iteam1/jetboy/docs/assets/imgs/img3.png

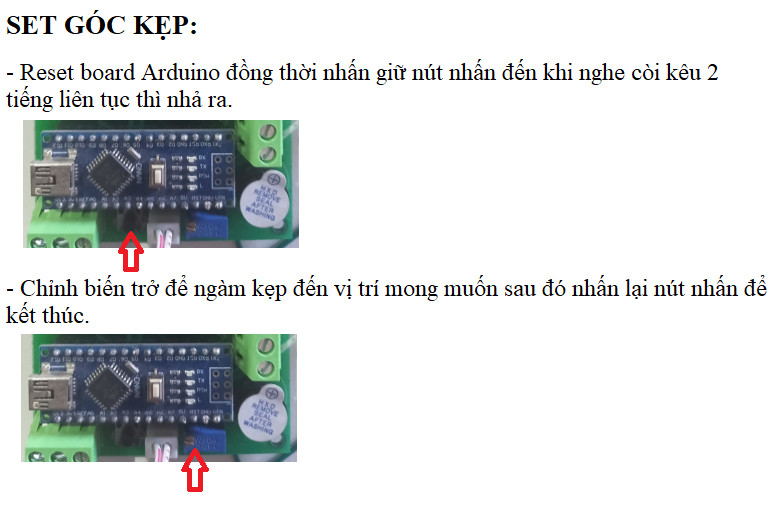
docs/assets/imgs/img3.png
