iteam1/jetboy/docs/assets/imgs/img4.png

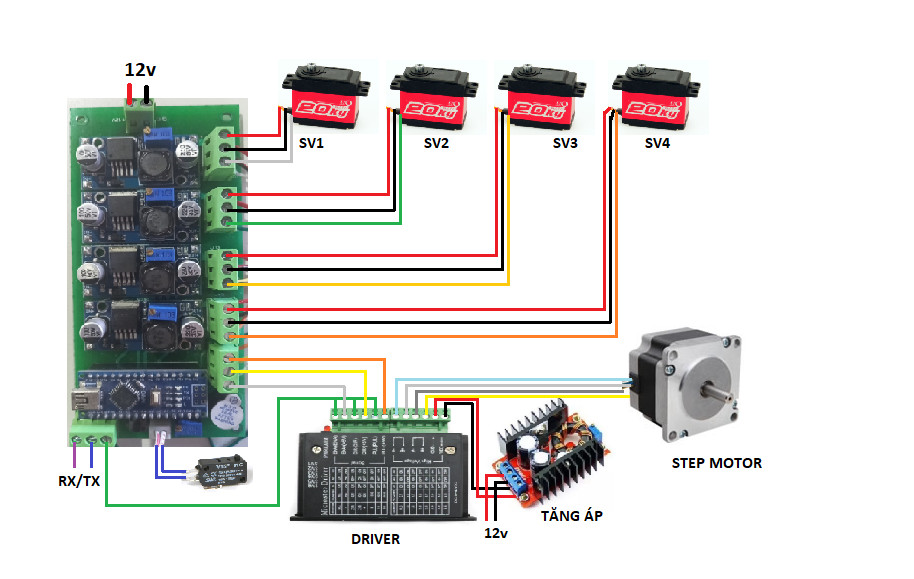
docs/assets/imgs/img4.png
