iteam1/jetboy/docs/assets/imgs/img5.png

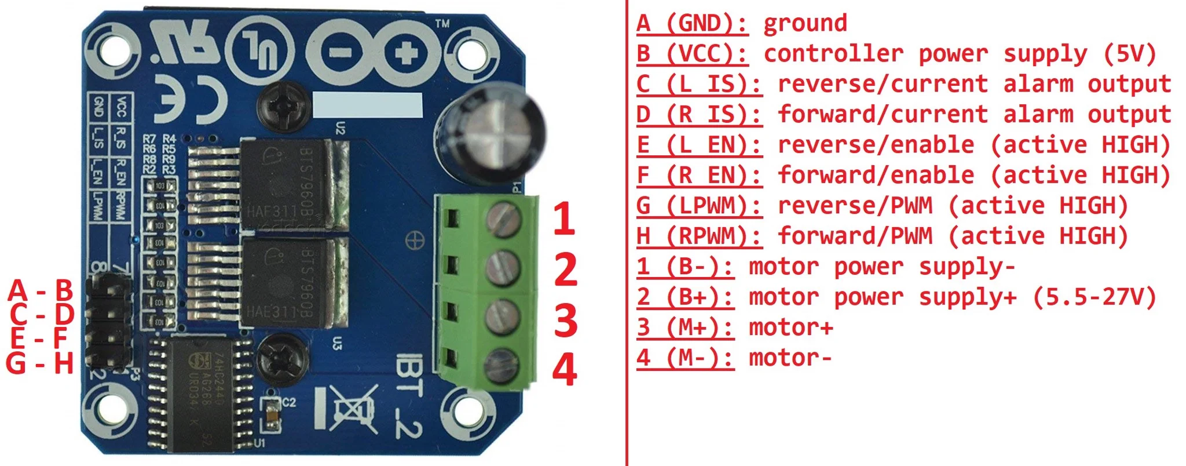
docs/assets/imgs/img5.png
