iteam1/jetboy/docs/assets/imgs/img6.png

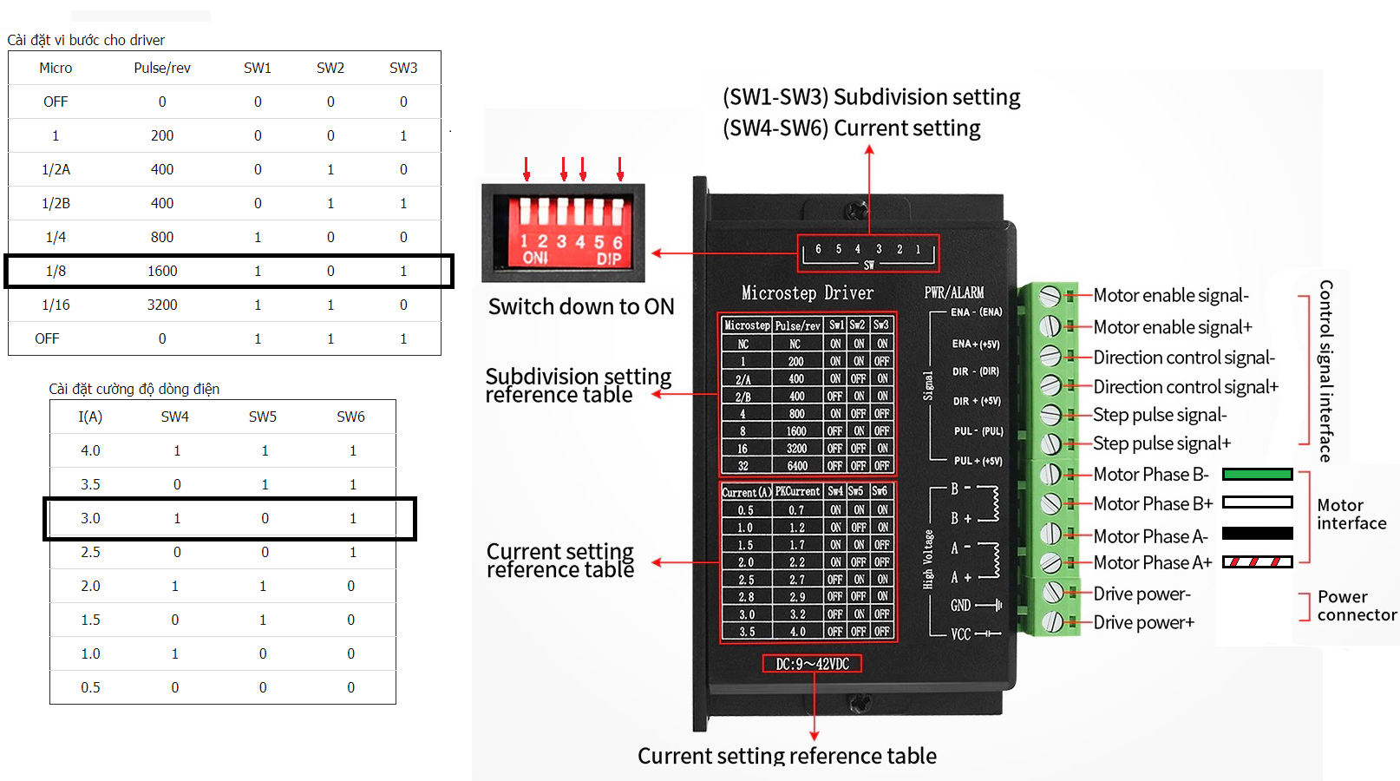
docs/assets/imgs/img6.png
