iteam1/jetboy/docs/assets/imgs/img7.png

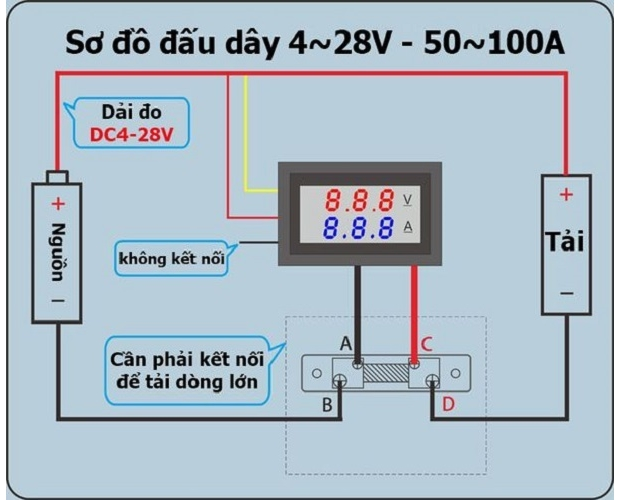
docs/assets/imgs/img7.png
