iteam1/jetboy/docs/assets/imgs/img8.png

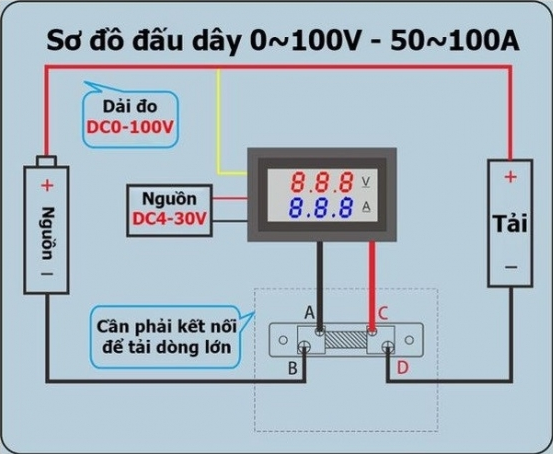
docs/assets/imgs/img8.png
