iteam1/jetboy/docs/assets/imgs/img9.png

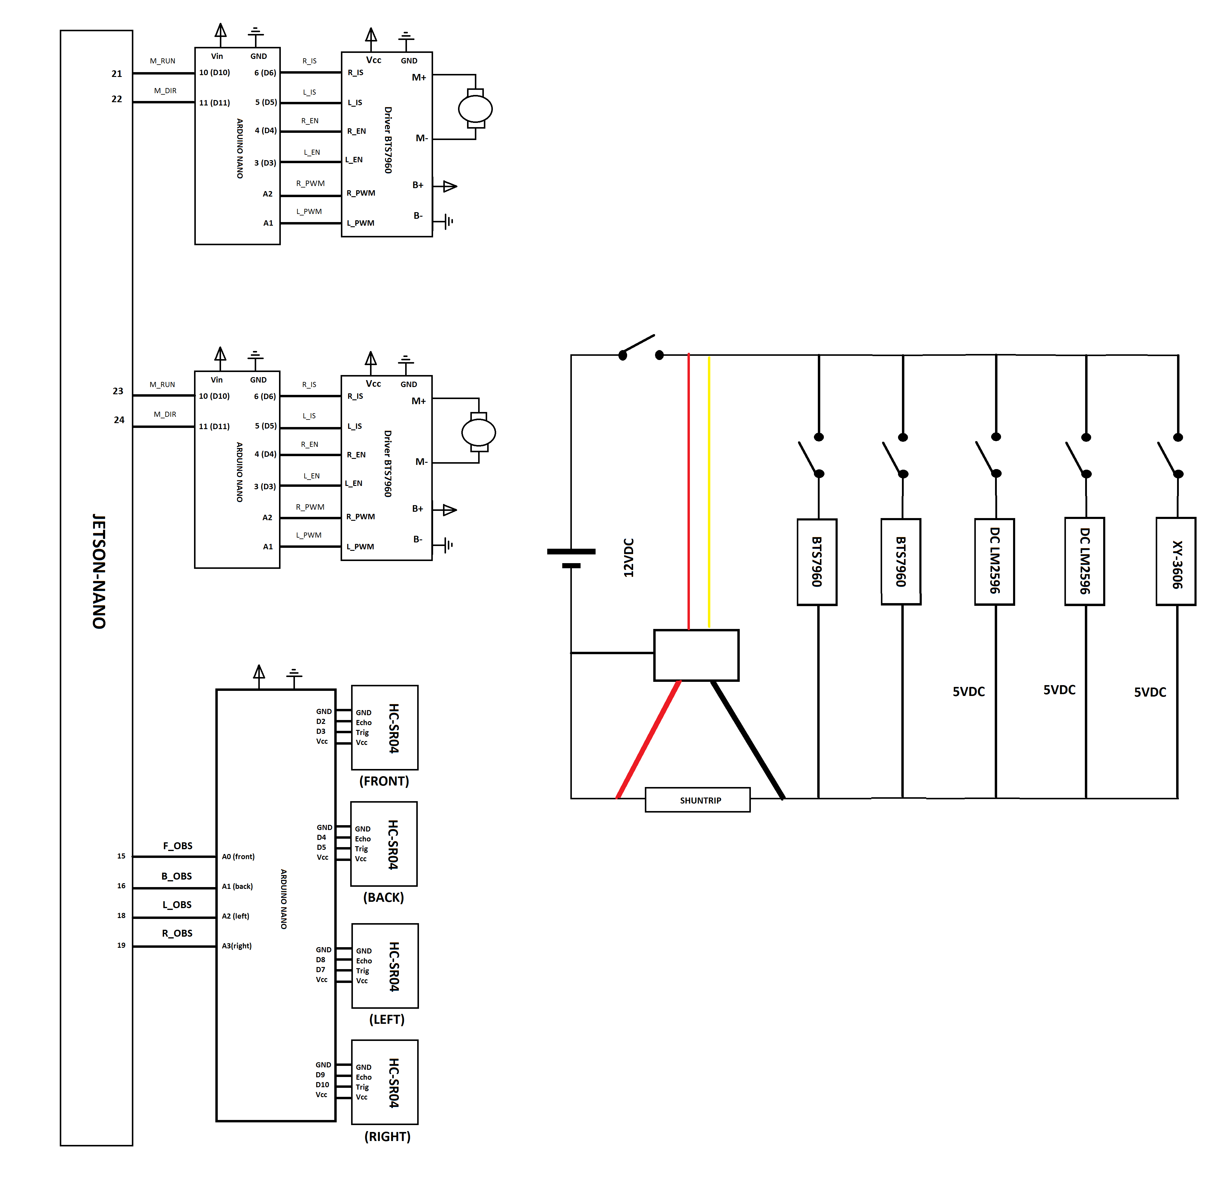
docs/assets/imgs/img9.png
