iteam1/jetboy/docs/assets/imgs/img10.png

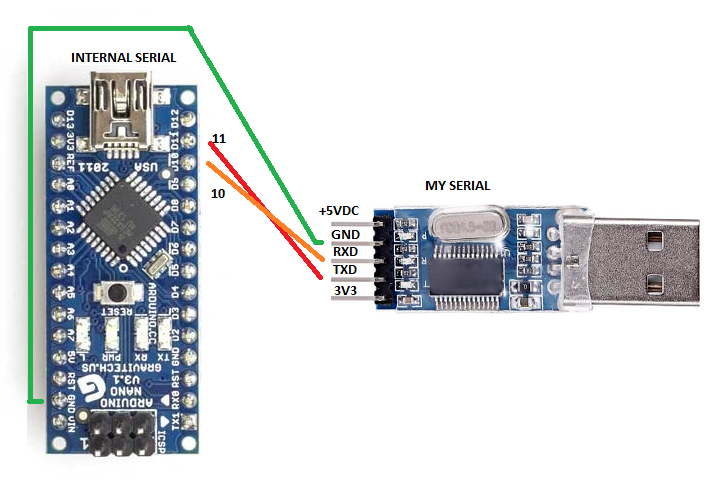
docs/assets/imgs/img10.png
