iteam1/jetboy/docs/assets/imgs/img11.png

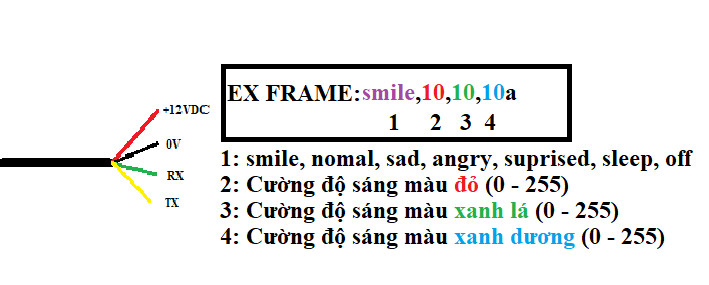
docs/assets/imgs/img11.png
