iteam1/jetboy/helloworlds.py

'''
Author: locchuong
Updated: 13/9/22
Description:
    Simple program for testing looping execution
'''
from time import sleep

def main():
	while True:
		print("Jetboy hello World!")
		sleep(1)

if __name__ == "__main__":
	
	main()
