iteam1/jetboy/robot/gendata.py

"""
Author: locchuong
Updated: 27/12/21
Description:
	If you don't have a database, first you create the database table by this program,
	'''
		from robot import db
		from robot.models import Robot
		robot = Robot()
		db.add(robot)
		db.commit()
	'''
	This program will create a new robot database, then flask server will connect to this database will a robot model

	1/ id: is the robot id (primary key)
	2/ name: robot's name

	# Control robot's action

	3/ command: This one will control the robot's action
		value: 
			- stop: robot will stop moving
			- forward: robot will moving forward
			- backward: robot will moving backward
			- turnleft: robot will turn left
			- turnright: robot will turn right
			- kill: terminate GPIO_controller while loop

		estop: value: 1-0, emergency stop, stop any moving if this bit is 1
		obs_f: value: 1-0, front obstacle
		obs_b: value: 1-0, back obstacle
		obs_l: value: 1-0, left obstacle
		obs_r: value: 1-0, right obstacle

	# Control robot's GUI display on the screen

	4/ content: the sentence content will display on the robot screen for TEXT,WORDS DISPLAY
	5/ emotion: the name of gif image will display on the robot screen for GIF,EMOTION DISPLAY
	6/ image: the name of the image will display on the robot screen for IMAGE DISPLAY
	7/ itype: the content's type will display on the robot
		value:
			- info: display content on the screen
			- emo: display emotion or gif on the screen
			- img: display the image on the screen
"""

import sqlite3 

conn = sqlite3.connect("site.db")

c = conn.cursor()

c.execute("""
	CREATE TABLE robot(
	id INTEGER PRIMARY KEY,
	name TEXT, 
	command TEXT,
	content TEXT,
	emotion TEXT,
	image TEXT,
	itype TEXT,
	estop NUMERIC,
	obs_f NUMERIC, 
	obs_b NUMERIC,
	obs_l NUMERIC,
	obs_r NUMERIC
	)
	""")

conn.commit()

print('Database created!')

conn.close()
